dan-lara/GouTupan/Hardware/PCB_Main_Board/Printed_PCB_v3_RECTO.png

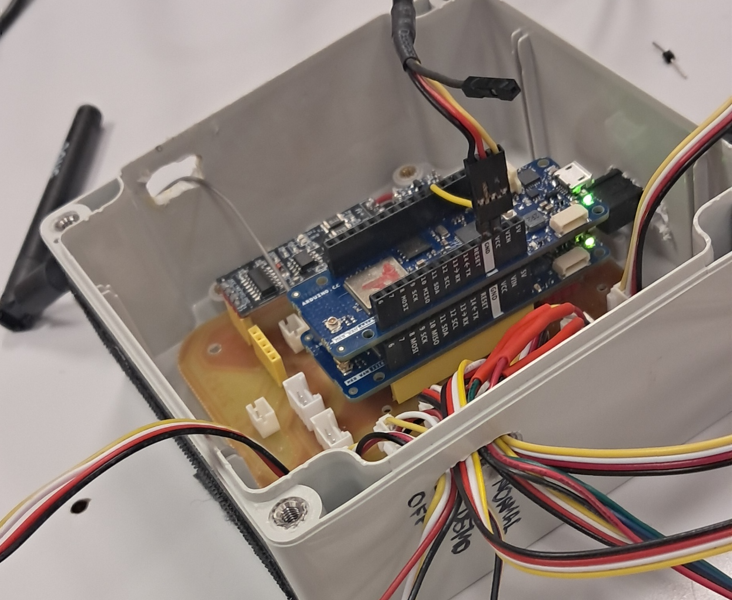
Hardware/PCB_Main_Board/Printed_PCB_v3_RECTO.png
