dan-lara/GouTupan/Hardware/PCB_Multi_Outside_Sensor_Onewire/Printed_PCB_v1_RECTO.png

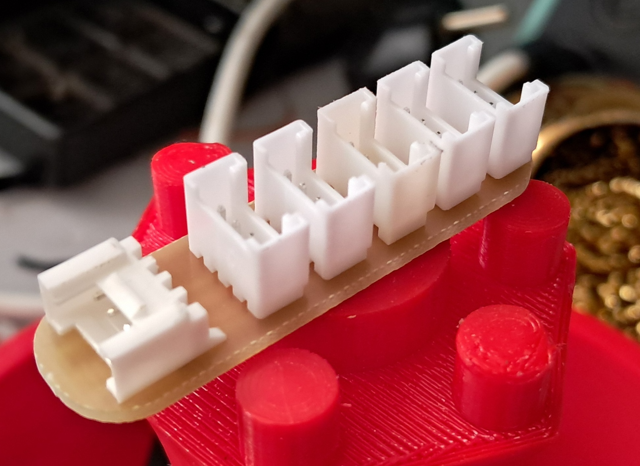
Hardware/PCB_Multi_Outside_Sensor_Onewire/Printed_PCB_v1_RECTO.png
