dan-lara/GouTupan/Hardware/PCB_Multi_Outside_Sensor_Onewire/Printed_PCB_v1_VERSO.png

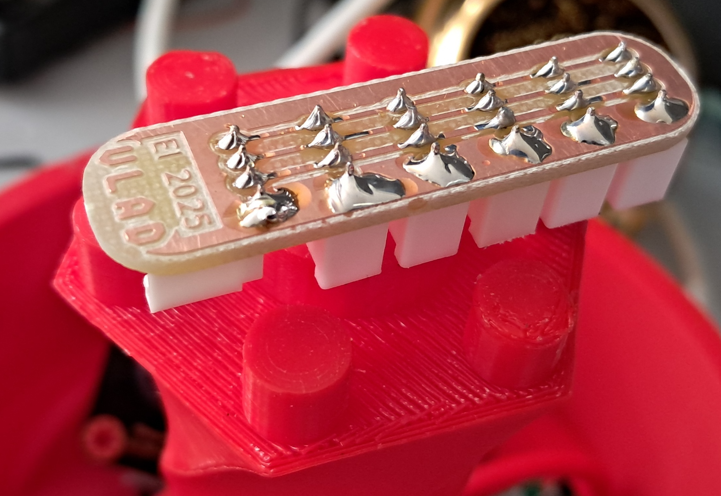
Hardware/PCB_Multi_Outside_Sensor_Onewire/Printed_PCB_v1_VERSO.png
