dan-lara/GouTupan/Firmware/epd2in9b_V3/epd2in9b_V3.ino

/**
 *  @filename   :   epd2in9b_V3-demo.ino
 *  @brief      :   2.9inch e-paper display demo
 *  @author     :   Waveshare
 *
 *  Copyright (C) Waveshare     Dec 3 2020
 *
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
 * THE SOFTWARE IS PROVIDED "AS IS", WITHOUT WARRANTY OF ANY KIND, EXPRESS OR
 * IMPLIED, INCLUDING BUT NOT LIMITED TO THE WARRANTIES OF MERCHANTABILITY,
 * FITNESS OR A PARTICULAR PURPOSE AND NONINFRINGEMENT. IN NO EVENT SHALL THE
 * AUTHORS OR COPYRIGHT HOLDERS BE LIABLE FOR ANY CLAIM, DAMAGES OR OTHER
 * LIABILITY WHETHER IN AN ACTION OF CONTRACT, TORT OR OTHERWISE, ARISING FROM,
 * OUT OF OR IN CONNECTION WITH THE SOFTWARE OR THE USE OR OTHER DEALINGS IN
 * THE SOFTWARE.
 */

#include <SPI.h>
#include "epd2in9b_V3.hpp"
#include "epd_text.hpp"

#define TEST_MODE 1
#define OPERATION_MODE 0

Epd epd;
EpdText epdText(epd);

void setup() {
  // put your setup code here, to run once:
  Serial.begin(115200);
  delay(2000);

  #if TEST_MODE
  Serial.print("2.9inch b V3 e-Paper init \r\n ");
  Serial.print("2.9inch b V3 e-Paper init \r\n ");
  Serial.print("2.9inch b V3 e-Paper init \r\n ");
  #endif

  if (epd.Init() != 0) {
      #if TEST_MODE
        Serial.print("e-Paper init failed\r\n ");
      #endif
      return;
  }
  
    #if TEST_MODE
      Serial.print("e-Paper Clear\r\n ");
    #endif
    epd.Clear();

  // 显示法语文本（带换行）
  //epdText.displayText("AABCDEFGZz\n00123456789");
  #if OPERATION_MODE
  delay(2000);
  epdText.updateDisplay(0, 23.4, 450.0, 40.2, 85.6,
                      10, 5, 12,
                      25.0, 45.0,
                      22.3, 47.5,
                      600, 100, 30,
                      255, 128, 64,
                      1013, 80, 20.9,
                      0.1, 2.3, 0.5, 0.7, 0.6, 1.0, 0.2, 0.3);
  #endif
}

void loop() {
  // put your main code here, to run repeatedly:
  
}
