dan-lara/GouTupan/Firmware/MAIN/epdif.cpp

#include "epdif.hpp"
#include <SPI.h>

EpdIf::EpdIf() {
};

EpdIf::~EpdIf() {
};

void EpdIf::DigitalWrite(int pin, int value) {
    digitalWrite(pin, value);
}

int EpdIf::DigitalRead(int pin) {
    return digitalRead(pin);
}

void EpdIf::DelayMs(unsigned int delaytime) {
    delay(delaytime);
}

void EpdIf::SpiTransfer(unsigned char data) {
    digitalWrite(CS_PIN, LOW);
    SPI.transfer(data);
    digitalWrite(CS_PIN, HIGH);
}

int EpdIf::IfInit(void) {
    pinMode(CS_PIN, OUTPUT);
    pinMode(RST_PIN, OUTPUT);
    pinMode(DC_PIN, OUTPUT);
    pinMode(BUSY_PIN, INPUT); 

    pinMode(PWR_PIN, OUTPUT);
    DigitalWrite(PWR_PIN, 1);

    SPI.begin();
    SPI.beginTransaction(SPISettings(2000000, MSBFIRST, SPI_MODE0));
    return 0;
}
